jspolsky/Antenna2024/Whips-PCB/turtle-art/original.png

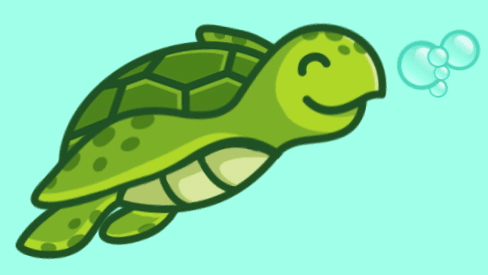
Whips-PCB/turtle-art/original.png
