jspolsky/Antenna2024/Whips-PCB/turtle-art/pieces/FCu BCu.png

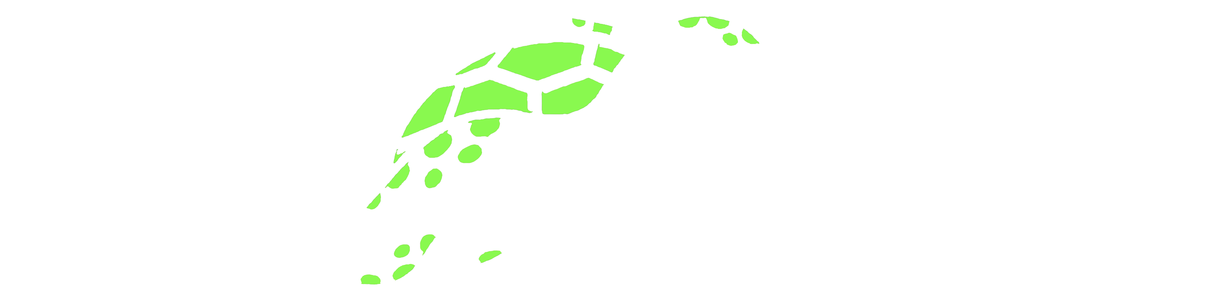
Whips-PCB/turtle-art/pieces/FCu BCu.png
