jspolsky/Antenna2024/Whips-PCB/turtle-art/pieces/FCu FMask BCu BMask.png

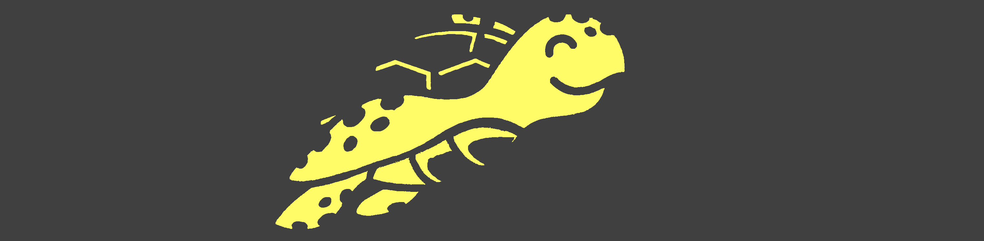
Whips-PCB/turtle-art/pieces/FCu FMask BCu BMask.png
