jspolsky/Antenna2024/Whips-PCB/turtle-art/pieces/FMask BMask.png

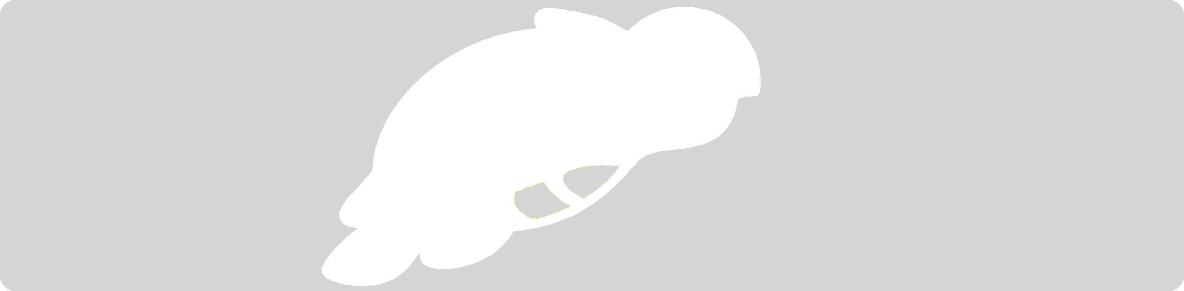
Whips-PCB/turtle-art/pieces/FMask BMask.png
