jspolsky/Antenna2024/Whips-PCB/turtle-art/pieces/FSilk BSilk.png

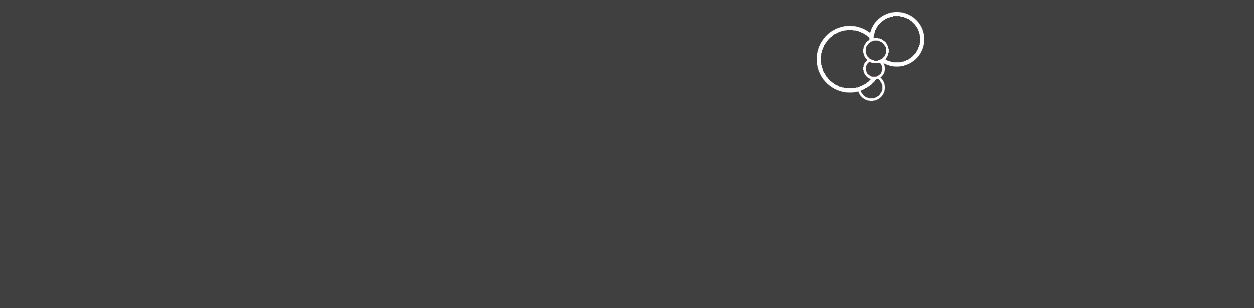
Whips-PCB/turtle-art/pieces/FSilk BSilk.png
