jspolsky/Antenna2024/Whips-PCB/turtle-art/quantized.png

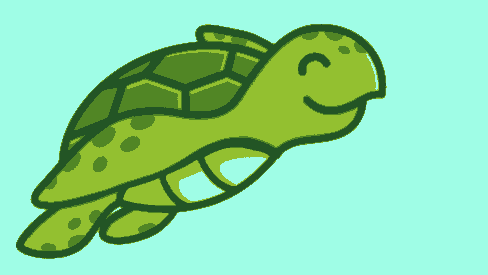
Whips-PCB/turtle-art/quantized.png
